ebyerly/openwrite/_datasheets/KeeBoar_sch.png

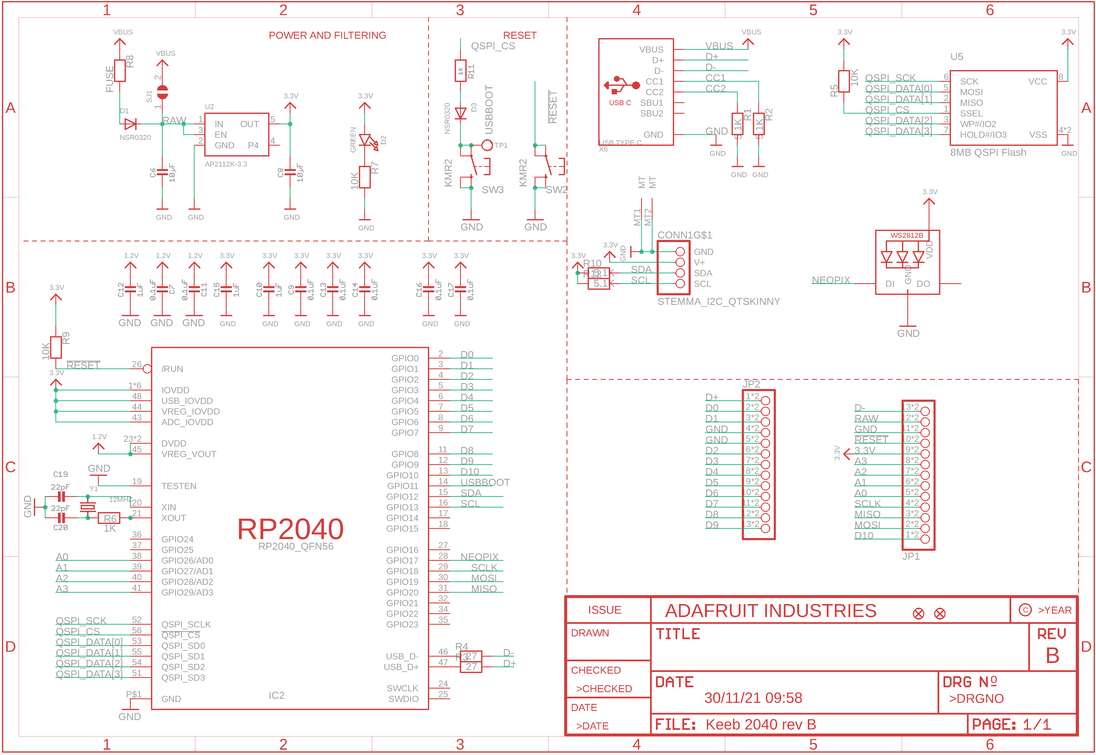
_datasheets/KeeBoar_sch.png
